bnich/chaojie-touchscreen-gen4/renders/gen4-arm.png

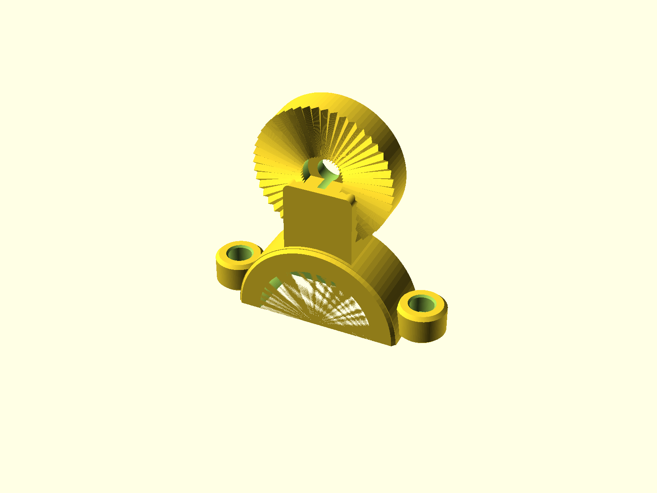
renders/gen4-arm.png
