bnich/chaojie-touchscreen-gen4/renders/gen4-gauge.png

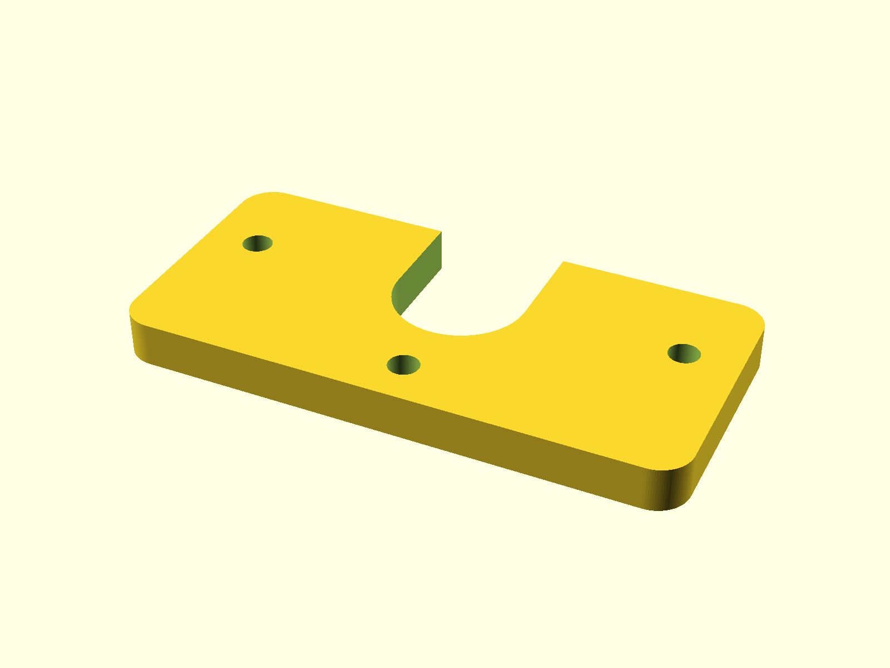
renders/gen4-gauge.png
