bnich/chaojie-touchscreen-gen4/renders/gen4-visor-profile.png

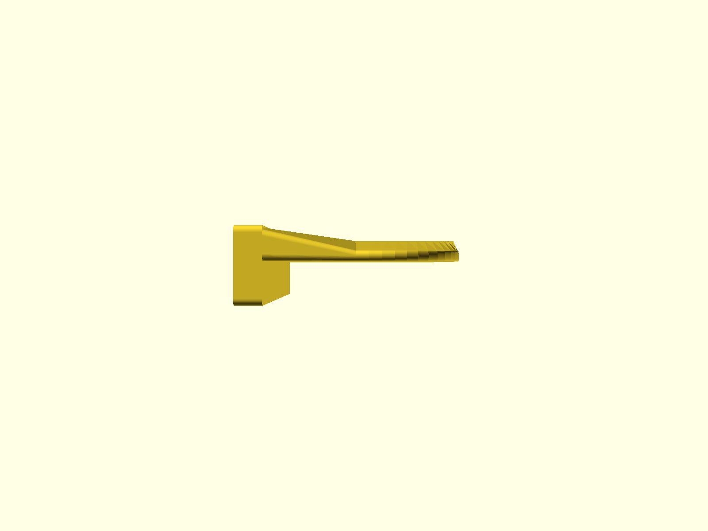
renders/gen4-visor-profile.png
