bnich/chaojie-touchscreen-gen4/renders/gen4-assembly-side.png

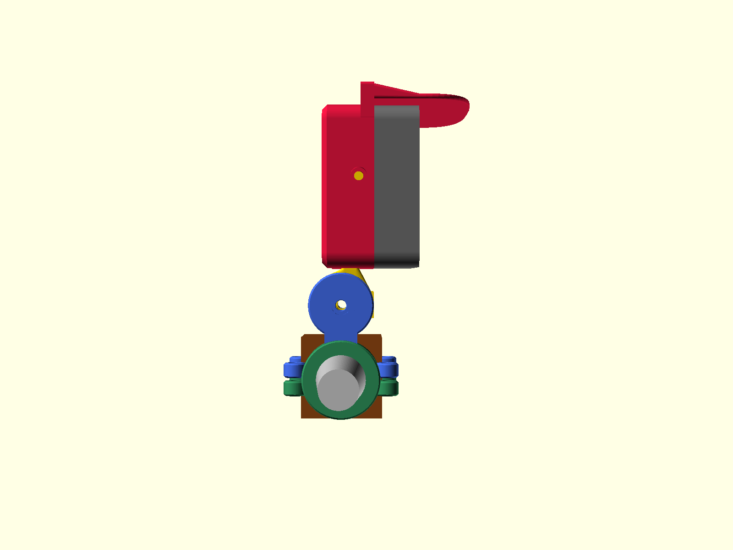
renders/gen4-assembly-side.png
