bnich/chaojie-touchscreen-gen4/renders/gen4-brow-test.png

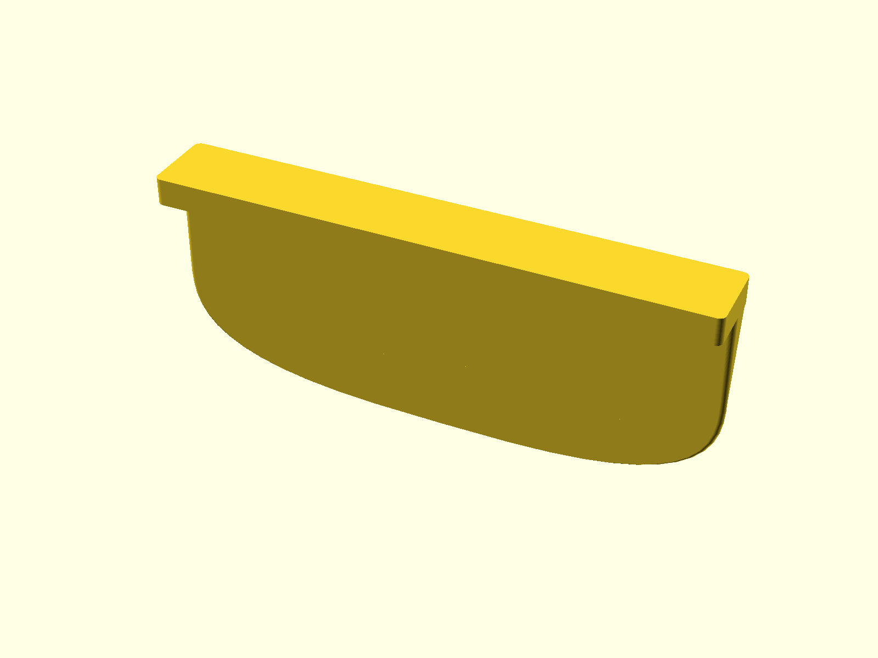
renders/gen4-brow-test.png
