bnich/chaojie-touchscreen-gen4/renders/gen4-spline-test.png

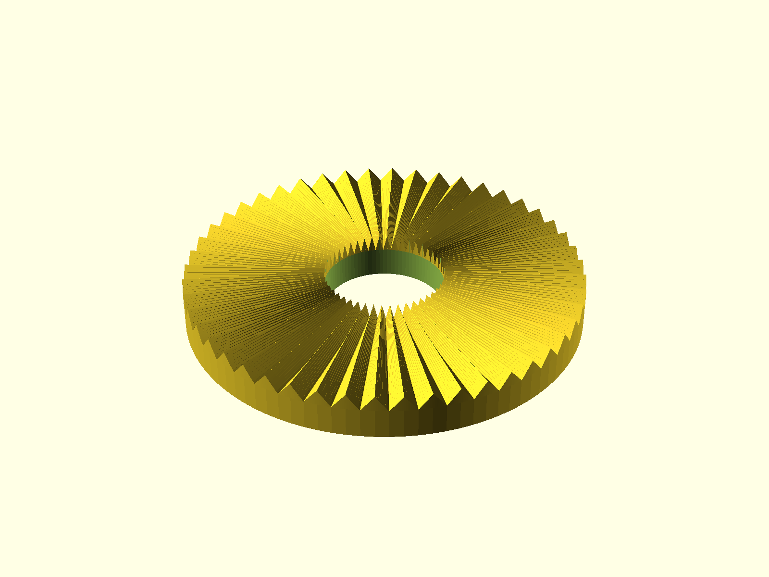
renders/gen4-spline-test.png
